ricardovgodoy/HiveBoard/CAD/Button/Button_Base.step

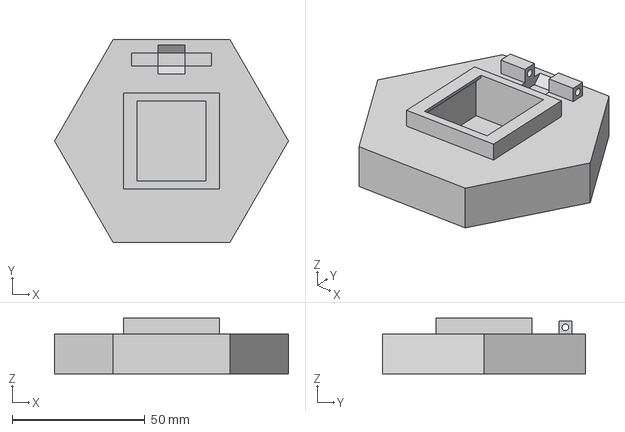
[picture p19: CAD file, 2026-05-12]
CAD/Button/Button_Base.step
88.1 x 76.3 x 21.0 mm
