ricardovgodoy/HiveBoard/CAD/Circuit Breaker/Circuit_Breaker_Switch.step

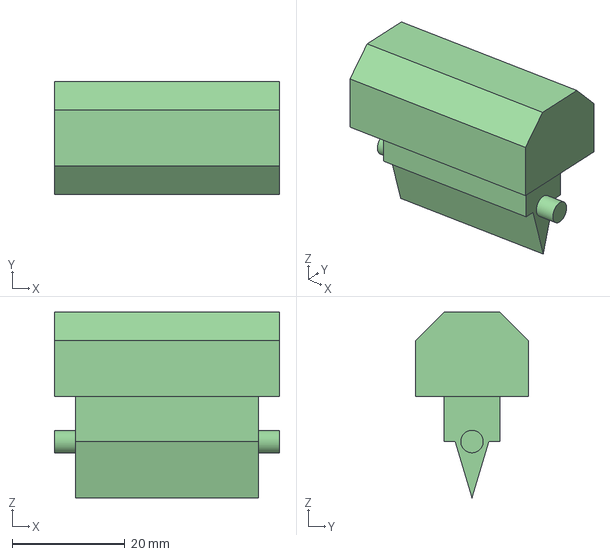
[picture p20: CAD file, 2026-05-12]
CAD/Circuit Breaker/Circuit_Breaker_Switch.step
40.0 x 20.0 x 33.0 mm
