ricardovgodoy/HiveBoard/CAD/Drawer/Drawer_Base.step

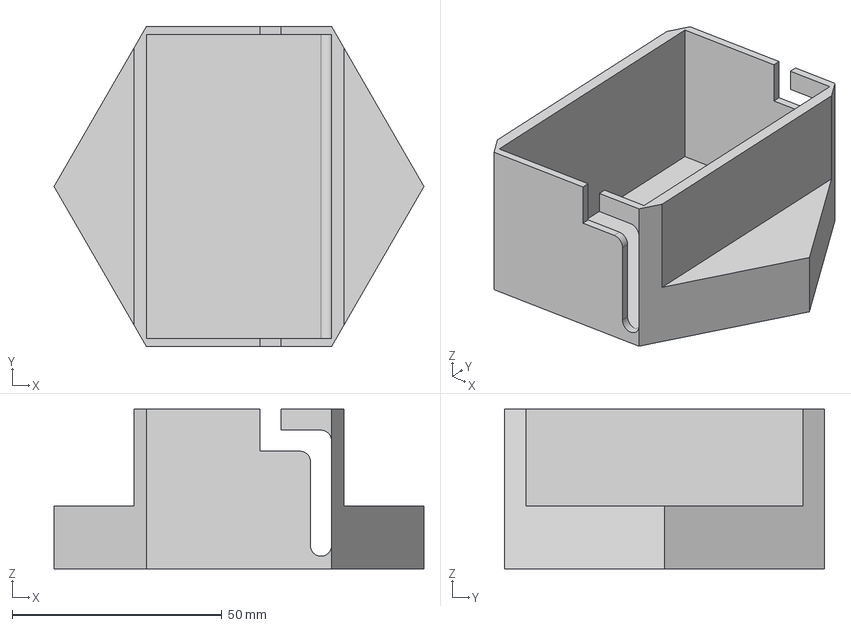
[picture p21: CAD file, 2026-05-12]
CAD/Drawer/Drawer_Base.step
88.1 x 76.3 x 38.0 mm
