ricardovgodoy/HiveBoard/CAD/Honeycomb/Honeycomb.step

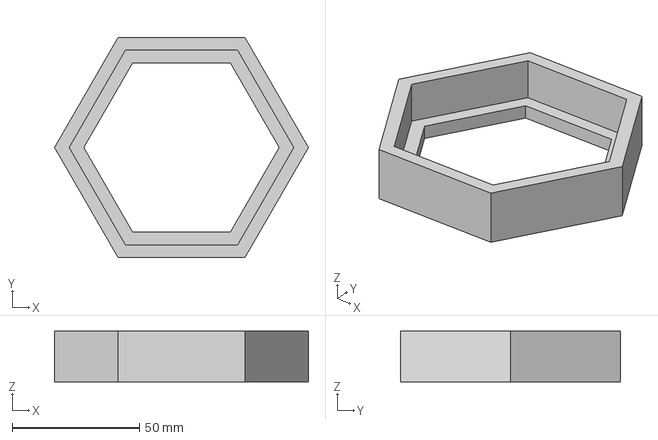
[picture p22: CAD file, 2026-05-12]
CAD/Honeycomb/Honeycomb.step
100.0 x 86.6 x 20.0 mm
