ricardovgodoy/HiveBoard/CAD/Key/Key_Base.step

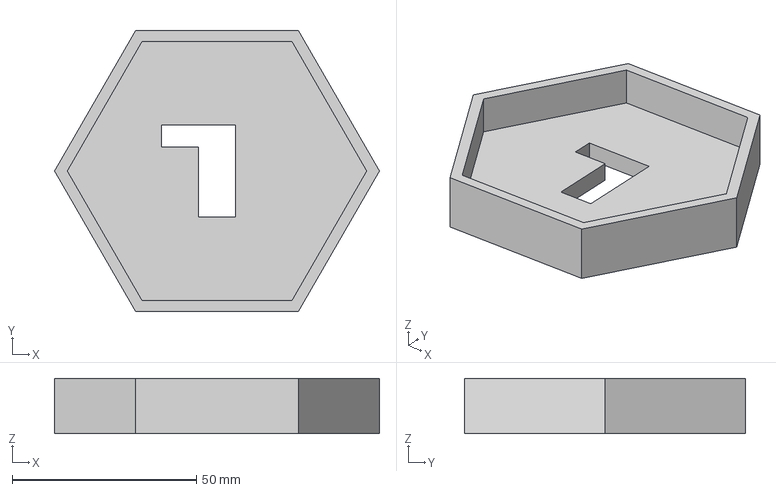
[picture p23: CAD file, 2026-05-12]
CAD/Key/Key_Base.step
88.1 x 76.3 x 15.0 mm
