ricardovgodoy/HiveBoard/CAD/Threads/M14 Thread/M14_Test.step

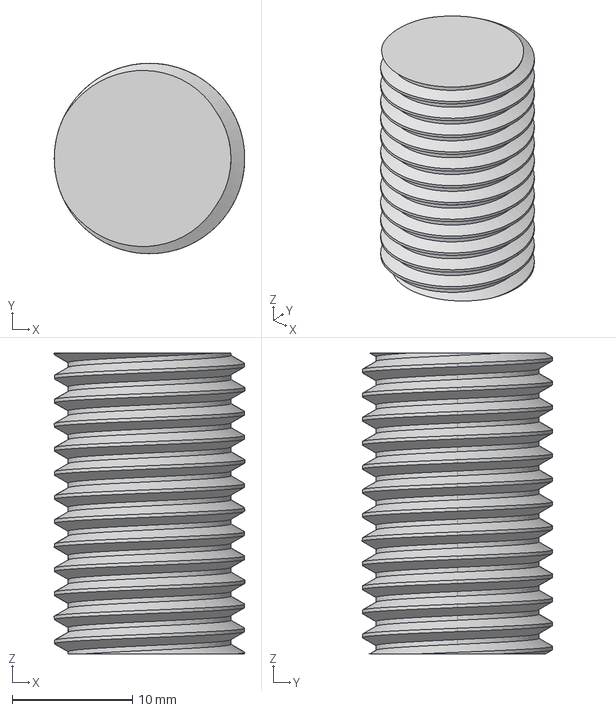
[picture p24: CAD file, 2026-05-12]
CAD/Threads/M14 Thread/M14_Test.step
15.8 x 15.8 x 25.0 mm
