ricardovgodoy/HiveBoard/CAD/Threads/M30 Thread/M30_Test.step

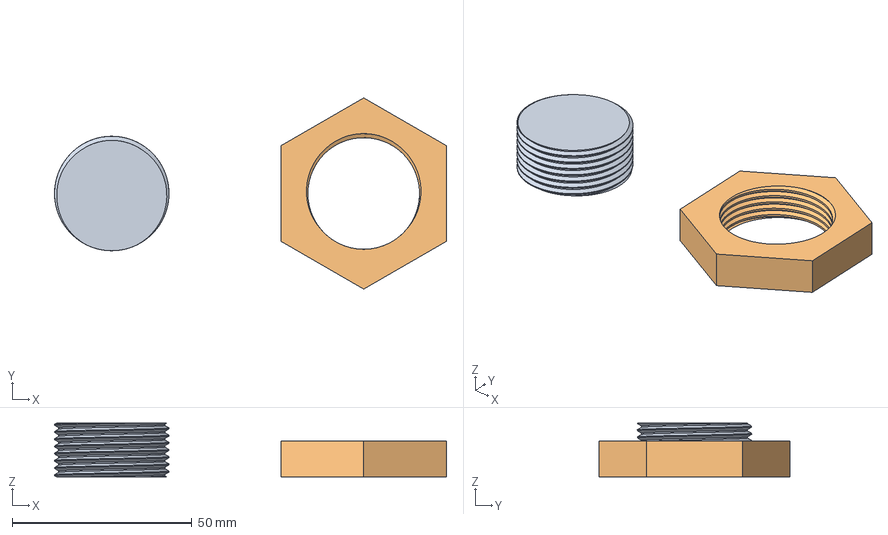
[picture p25: CAD file, 2026-05-12]
CAD/Threads/M30 Thread/M30_Test.step
108.9 x 53.1 x 15.0 mm
