ricardovgodoy/HiveBoard/CAD/Valves/Gate Valve/Small Valve/Small_Valve_Base.step

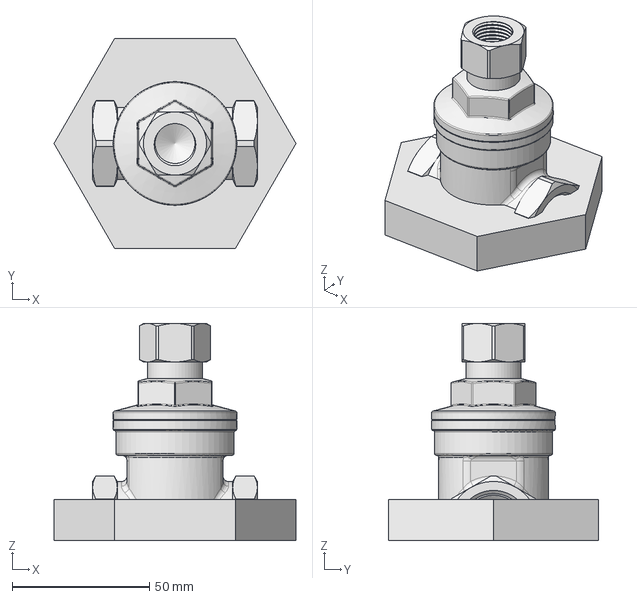
[picture p26: CAD file, 2026-05-12]
CAD/Valves/Gate Valve/Small Valve/Small_Valve_Base.step
88.1 x 76.3 x 79.0 mm
