ricardovgodoy/HiveBoard/CAD/Valves/Lever Valve/Ball Valve/Ball_Valve_Base.step

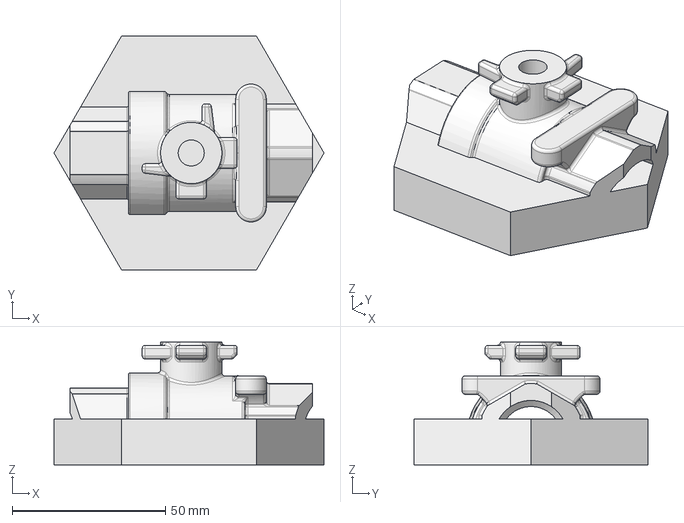
[picture p27: CAD file, 2026-05-12]
CAD/Valves/Lever Valve/Ball Valve/Ball_Valve_Base.step
88.1 x 76.3 x 40.0 mm
