ricardovgodoy/HiveBoard/CAD/Lamp/Lamp_Base.step

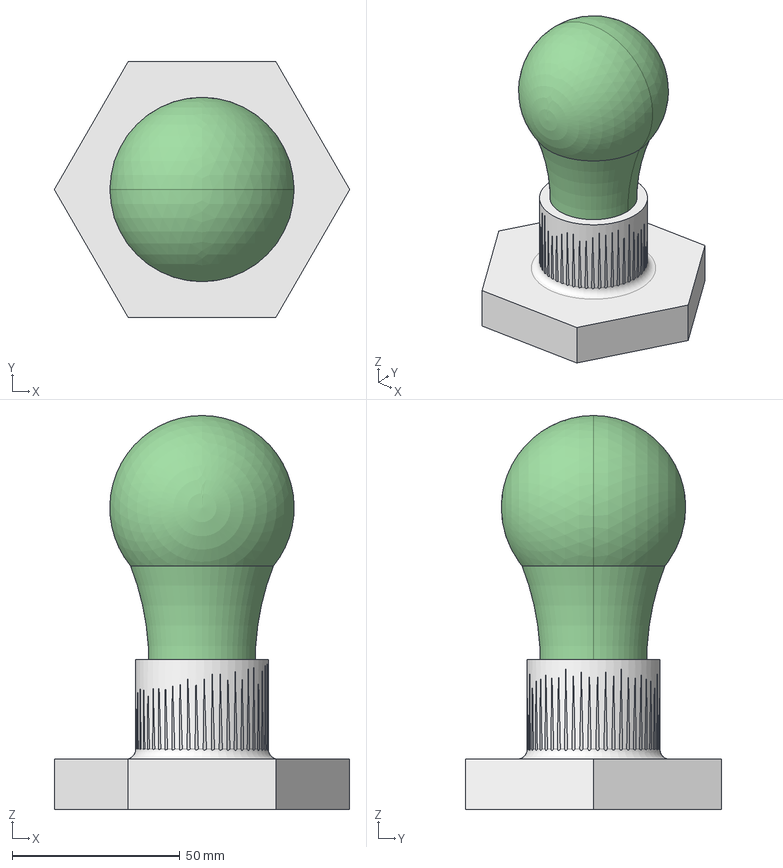
[picture p28: CAD file, 2026-05-12]
CAD/Lamp/Lamp_Base.step
88.1 x 76.3 x 117.5 mm
