ricardovgodoy/HiveBoard/CAD/Shock Absorber/Shock_Absorber_Pin.step

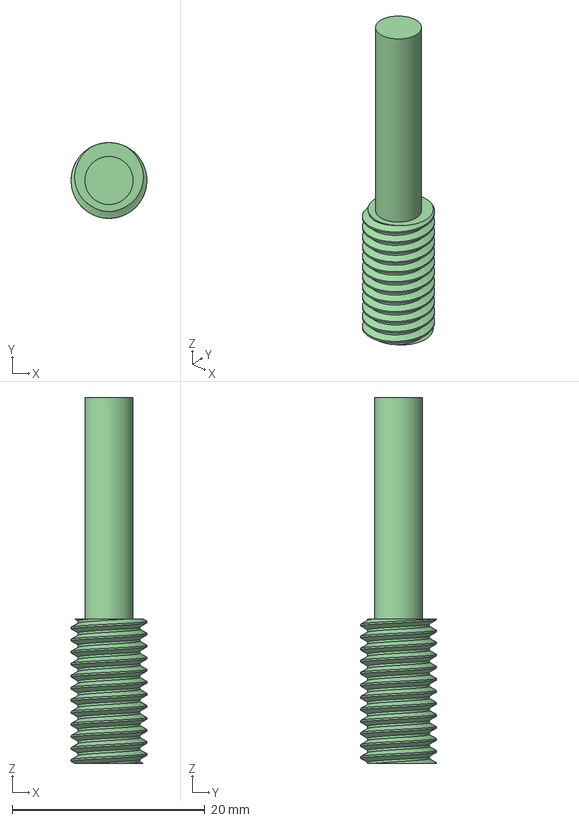
[picture p29: CAD file, 2026-05-12]
CAD/Shock Absorber/Shock_Absorber_Pin.step
7.88 x 7.88 x 38.0 mm
