ricardovgodoy/HiveBoard/CAD/Threads/M8 Thread/M8_Test.step

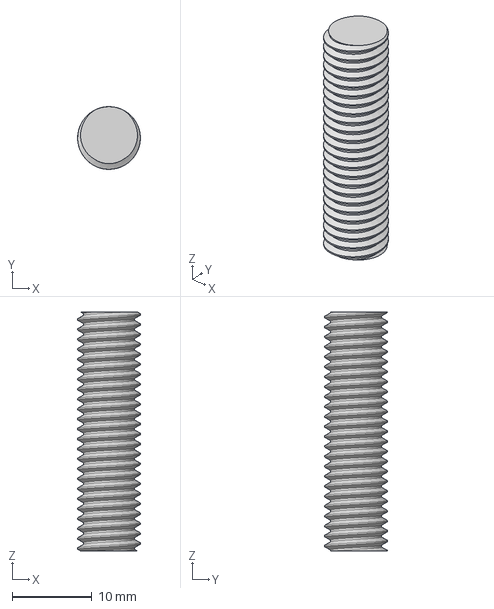
[picture p30: CAD file, 2026-05-12]
CAD/Threads/M8 Thread/M8_Test.step
7.88 x 7.88 x 30.0 mm
