ricardovgodoy/HiveBoard/CAD/Valves/Gate Valve/High Torque Valve/High_Torque_Valve_Base.step

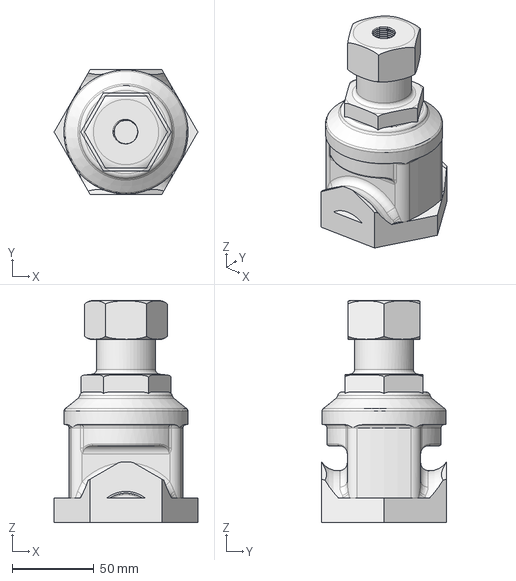
[picture p31: CAD file, 2026-05-12]
CAD/Valves/Gate Valve/High Torque Valve/High_Torque_Valve_Base.step
88.1 x 76.3 x 136.0 mm
