ricardovgodoy/HiveBoard/CAD/Valves/Lever Valve/Ball Valve/Ball_Valve_Lever.step

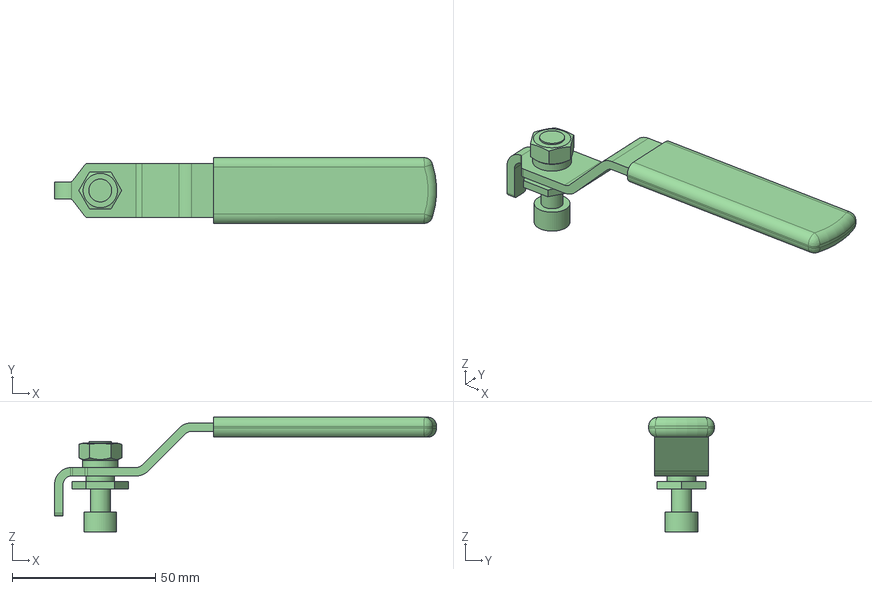
[picture p32: CAD file, 2026-05-12]
CAD/Valves/Lever Valve/Ball Valve/Ball_Valve_Lever.step
133.5 x 23.0 x 40.1 mm
