ricardovgodoy/HiveBoard/CAD/Button/Button_Spring.step

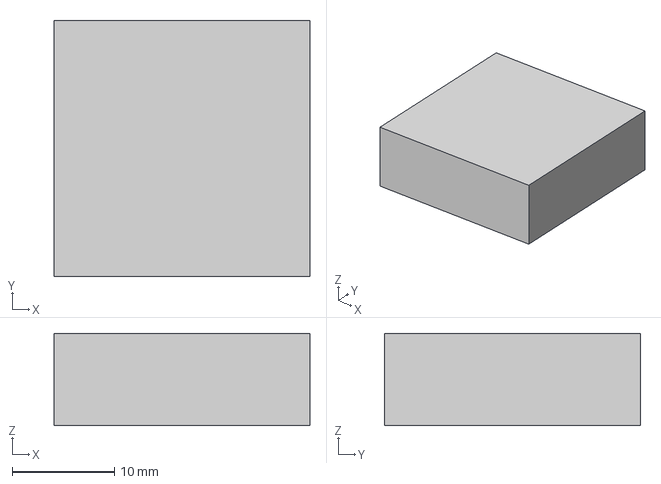
[picture p33: CAD file, 2026-05-12]
CAD/Button/Button_Spring.step
25.0 x 25.0 x 9.00 mm
