ricardovgodoy/HiveBoard/CAD/Shock Absorber/Shock_Absorber_Base.step

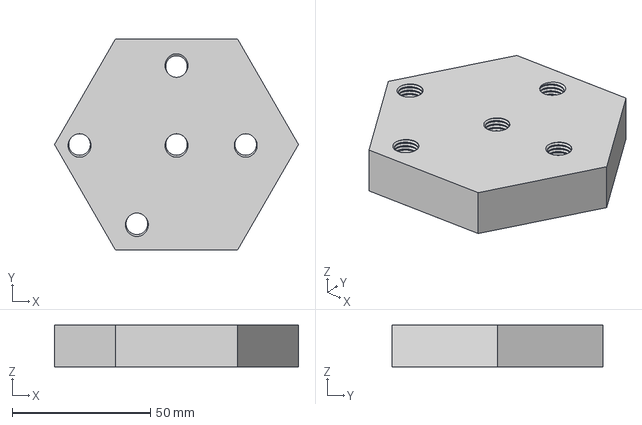
[picture p34: CAD file, 2026-05-12]
CAD/Shock Absorber/Shock_Absorber_Base.step
88.1 x 76.3 x 15.0 mm
