ricardovgodoy/HiveBoard/CAD/Valves/Lever Valve/Ball Valve/Ball_Valve_Friction_Ring_Set.step

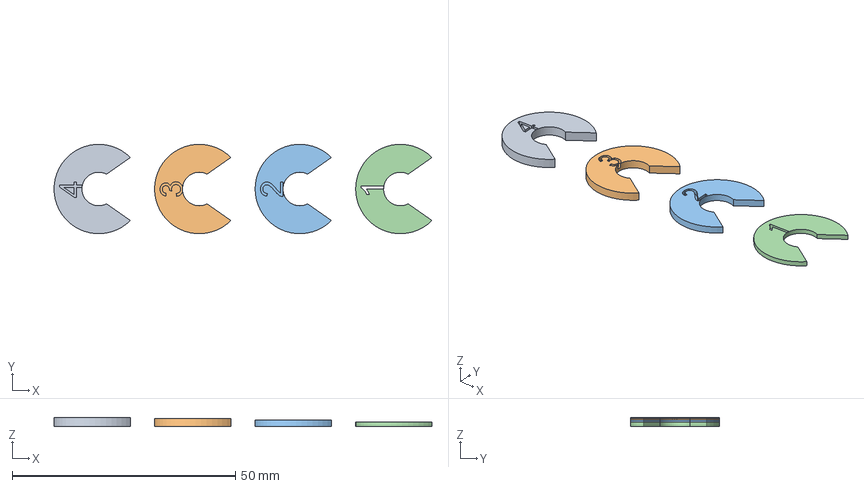
[picture p35: CAD file, 2026-05-12]
CAD/Valves/Lever Valve/Ball Valve/Ball_Valve_Friction_Ring_Set.step
84.6 x 20.0 x 2.00 mm
