ricardovgodoy/HiveBoard/CAD/Button/Button.step

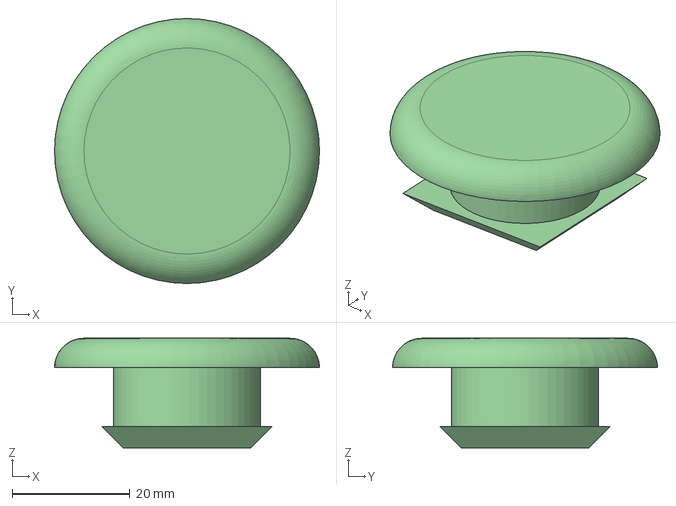
[picture p36: CAD file, 2026-05-12]
CAD/Button/Button.step
45.0 x 45.0 x 18.6 mm
