ricardovgodoy/HiveBoard/CAD/Shock Absorber/Shock_Absorber.step

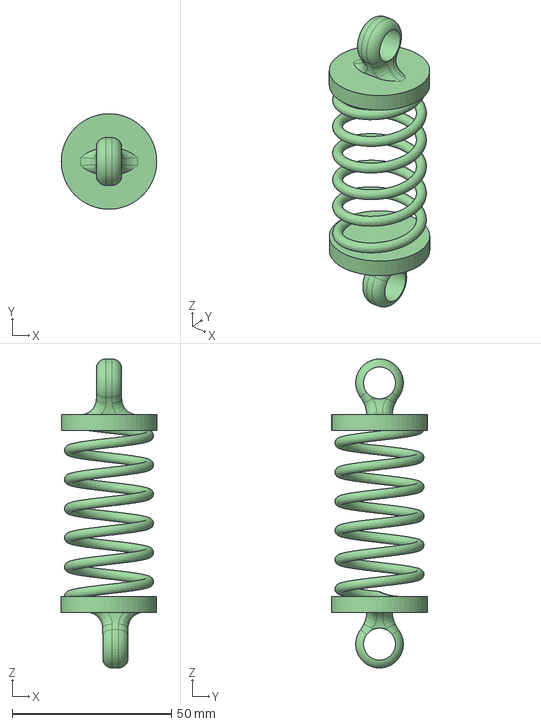
[picture p37: CAD file, 2026-05-12]
CAD/Shock Absorber/Shock_Absorber.step
30.0 x 30.0 x 97.0 mm
